RobotGrrl/Apisuru/3dprint/upper_lid_right.stl

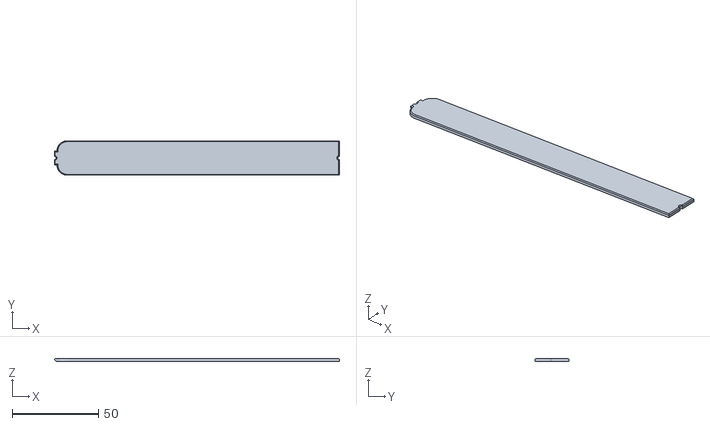
[picture p23: CAD file, 2025-02-03]
3dprint/upper_lid_right.stl
165.5 x 20.0 x 1.90
