RobotGrrl/Apisuru/3dprint/side_lid_upper_left.stl

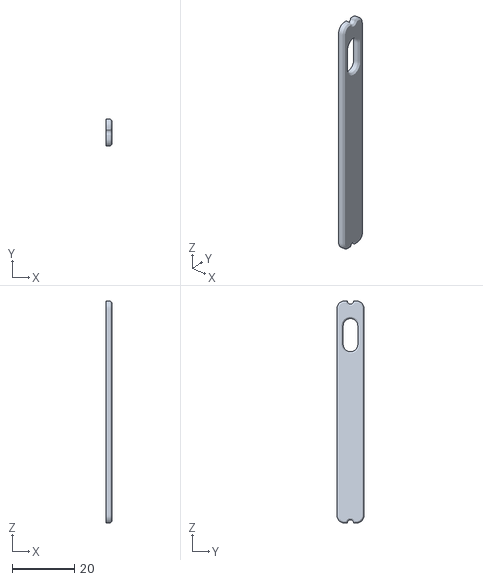
[picture p24: CAD file, 2025-02-03]
3dprint/side_lid_upper_left.stl
1.90 x 8.70 x 71.5
