RobotGrrl/Apisuru/3dprint/side_lid_lower_left.stl

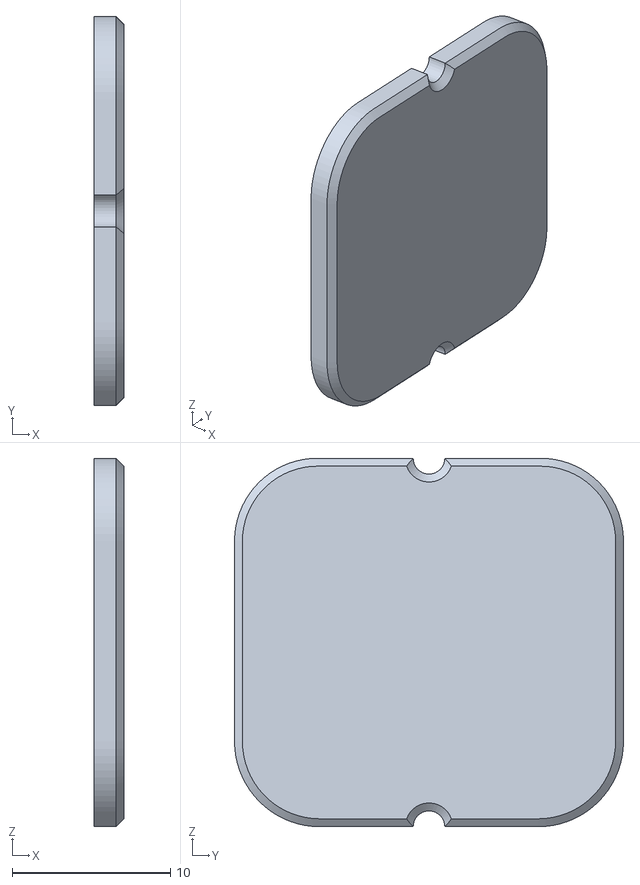
[picture p25: CAD file, 2025-02-03]
3dprint/side_lid_lower_left.stl
1.90 x 24.6 x 23.3
