RobotGrrl/Apisuru/3dprint/side_upper_right_F1B1.stl

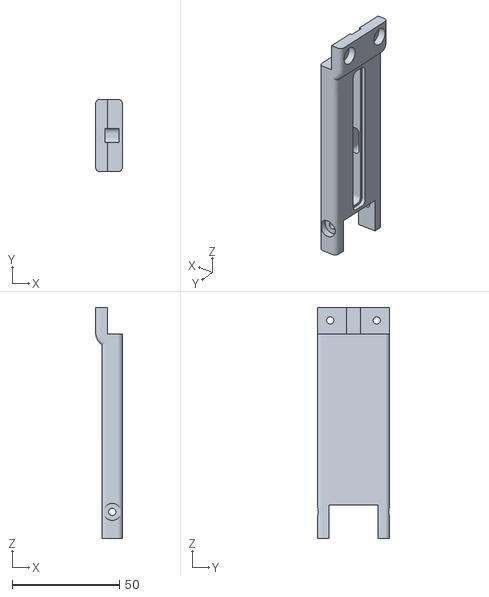
[picture p26: CAD file, 2025-02-03]
3dprint/side_upper_right_F1B1.stl
12.5 x 33.7 x 107.6
