RobotGrrl/Apisuru/3dprint/upper_lid_middle.stl

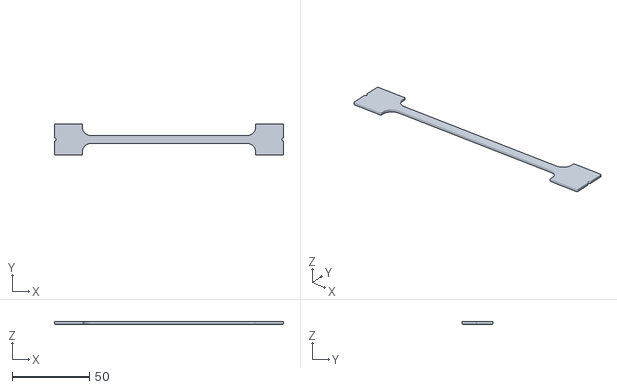
[picture p27: CAD file, 2025-02-03]
3dprint/upper_lid_middle.stl
148.0 x 20.0 x 1.90
