RobotGrrl/Apisuru/3dprint/upper_bar_middle_F0B0.stl

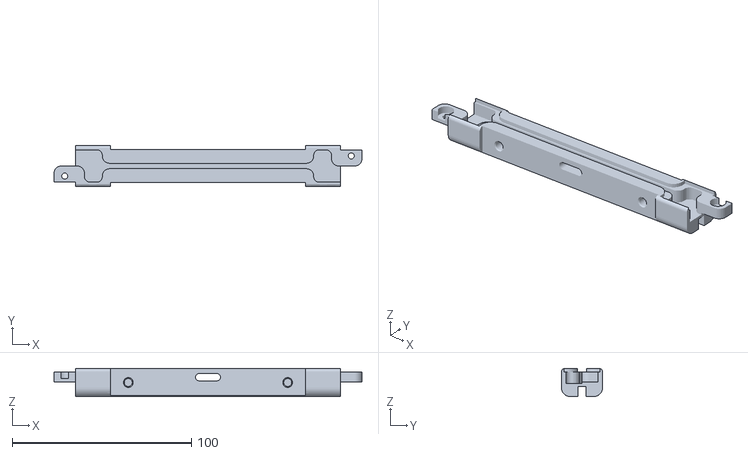
[picture p28: CAD file, 2025-02-03]
3dprint/upper_bar_middle_F0B0.stl
172.0 x 23.0 x 15.7
